ZimengXiong/sdcardthings/renders/sd-led-card-r0-bottom.png

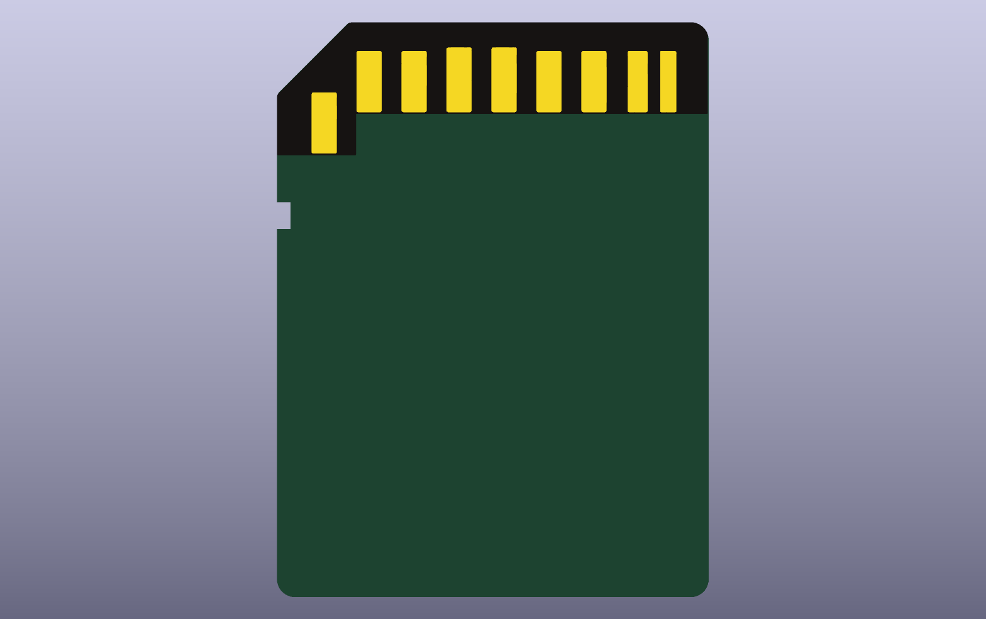
renders/sd-led-card-r0-bottom.png
