ZimengXiong/sdcardthings/renders/sd-led-card-r0.png

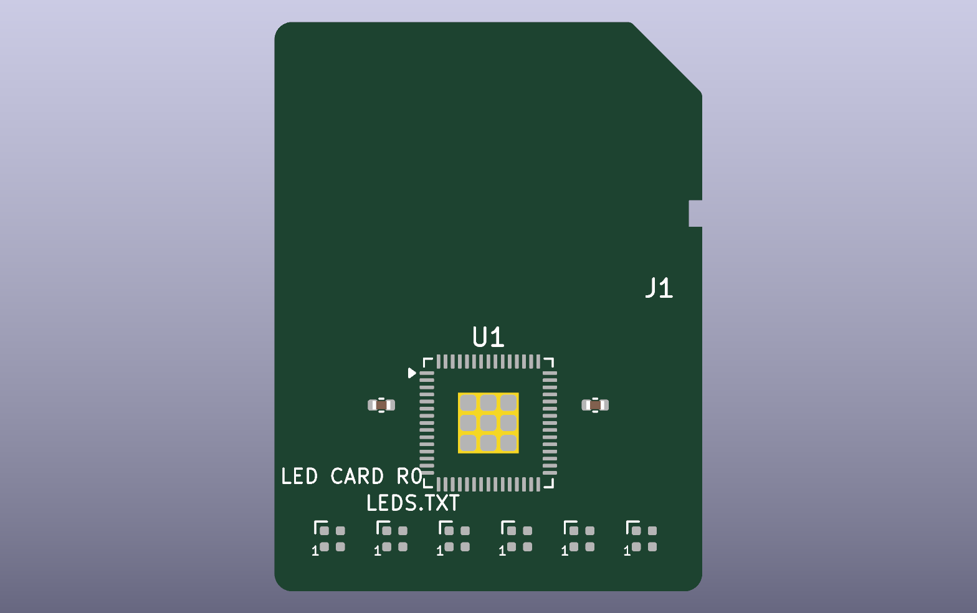
renders/sd-led-card-r0.png
