ZimengXiong/sdcardthings/renders/sd-led-card-r4-clean.png

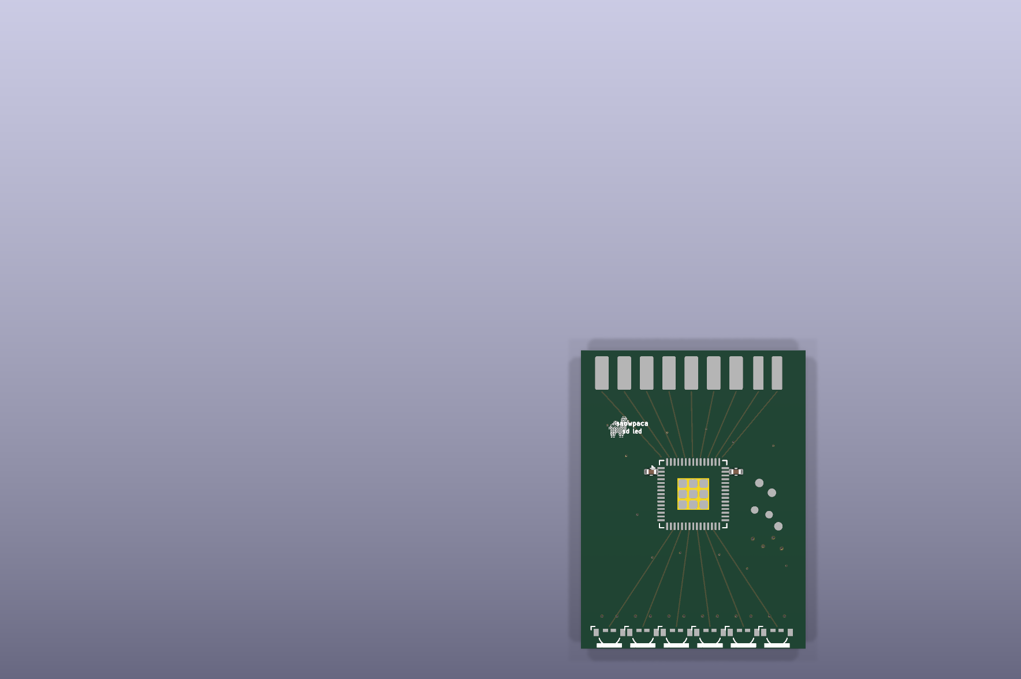
renders/sd-led-card-r4-clean.png
