ZimengXiong/sdcardthings/renders/sd-led-card-r6-full.png

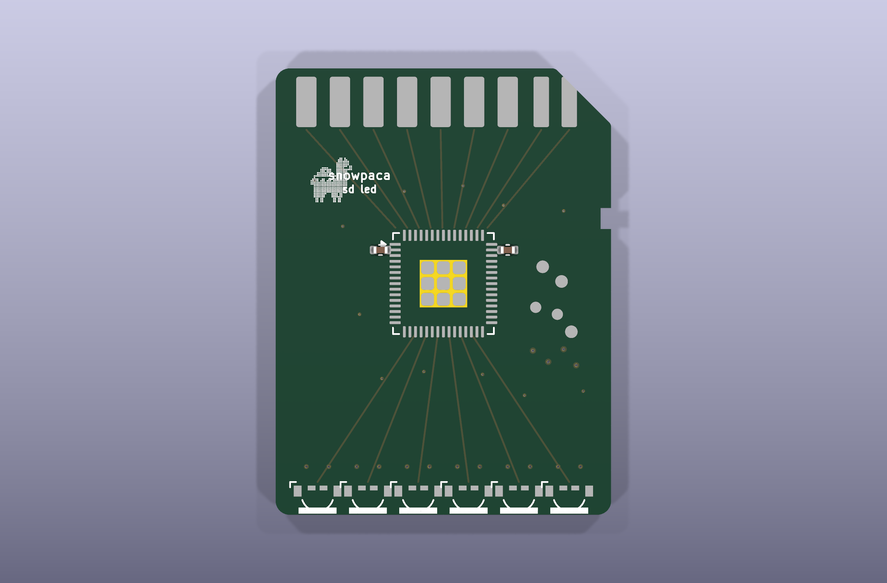
renders/sd-led-card-r6-full.png
