ZimengXiong/sdcardthings/renders/sd-led-card-r7-minimal.png

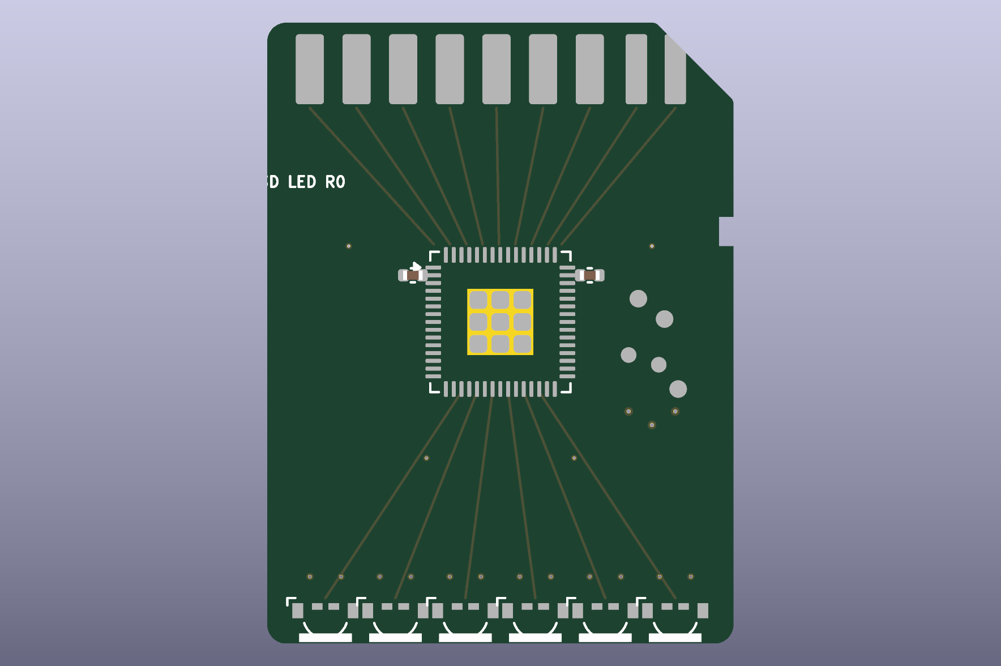
renders/sd-led-card-r7-minimal.png
