ZimengXiong/sdcardthings/renders/sd-led-card-r8-minimal-full.png

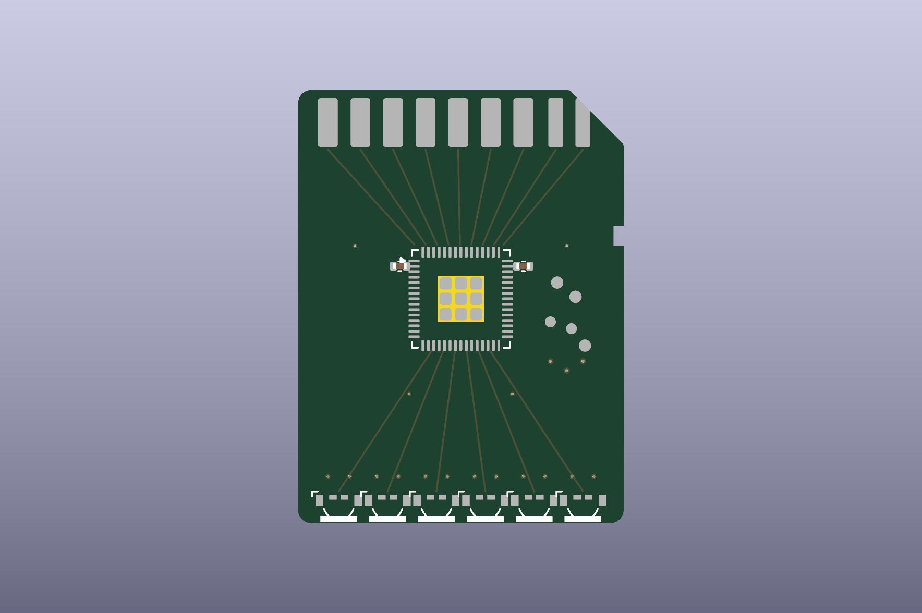
renders/sd-led-card-r8-minimal-full.png
