ZimengXiong/sdcardthings/renders/sd-led-card-r25-robot-up-top.png

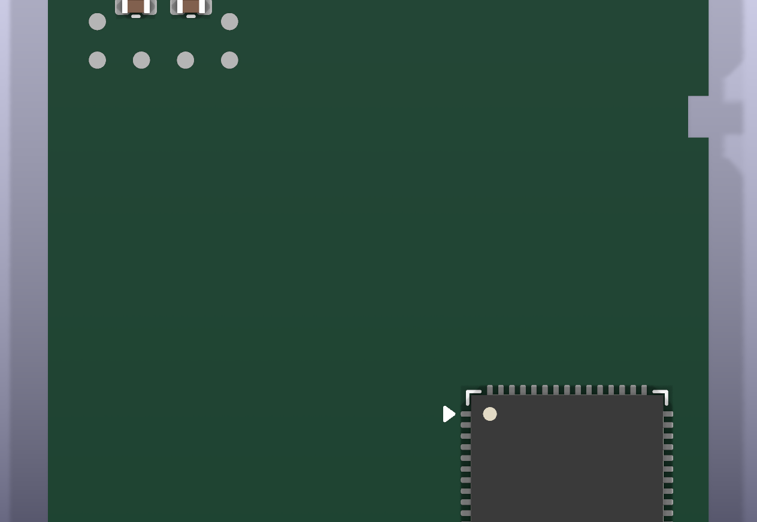
renders/sd-led-card-r25-robot-up-top.png
