ZimengXiong/sdcardthings/renders/sd-led-card-r26-full-top.png

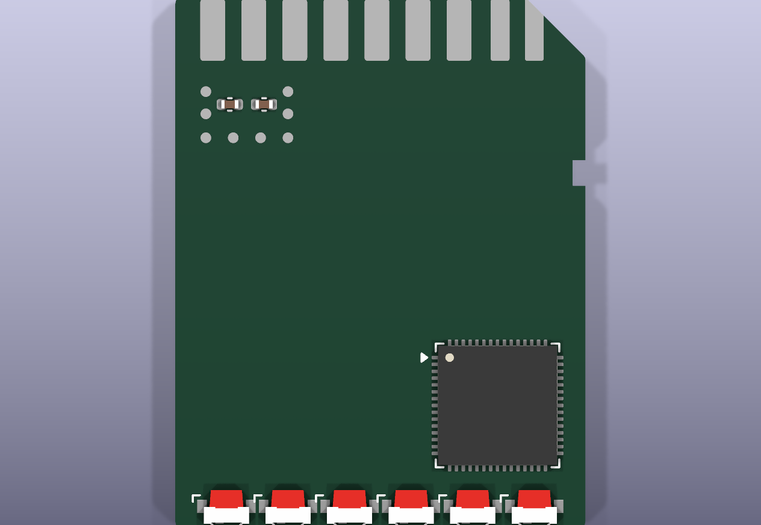
renders/sd-led-card-r26-full-top.png
