ZimengXiong/sdcardthings/renders/sd-led-card-r27-leds-closer-edge.png

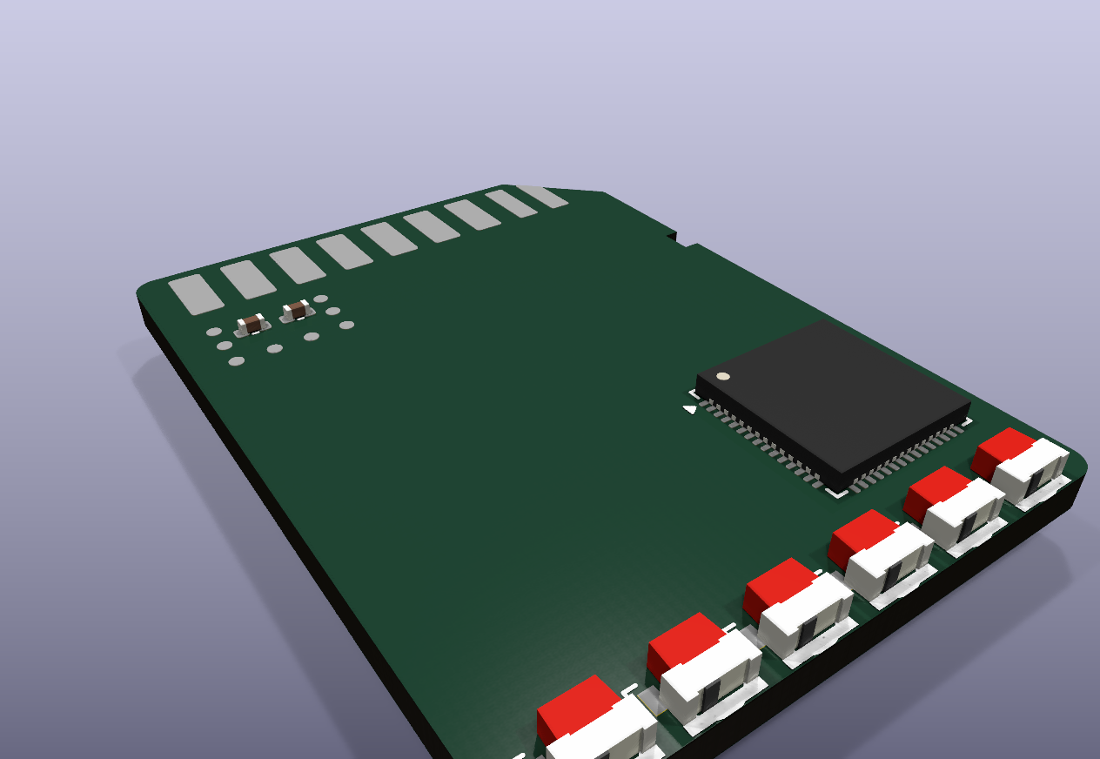
renders/sd-led-card-r27-leds-closer-edge.png
