ZimengXiong/sdcardthings/renders/sd-led-card-r33-cap-touch-contact-side-topdown.png

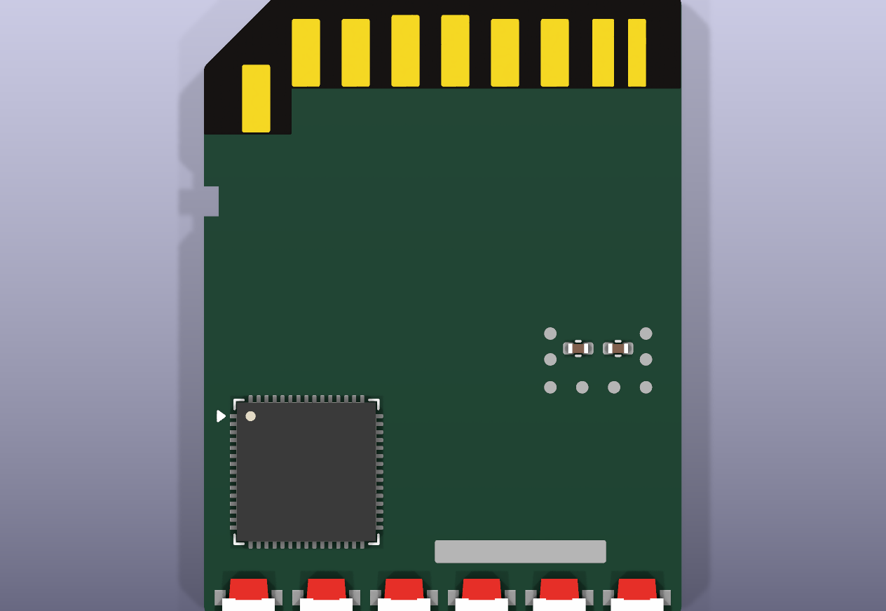
renders/sd-led-card-r33-cap-touch-contact-side-topdown.png
